iamthesoy/Project-Trousersnake/Images/IMG_2059.jpg

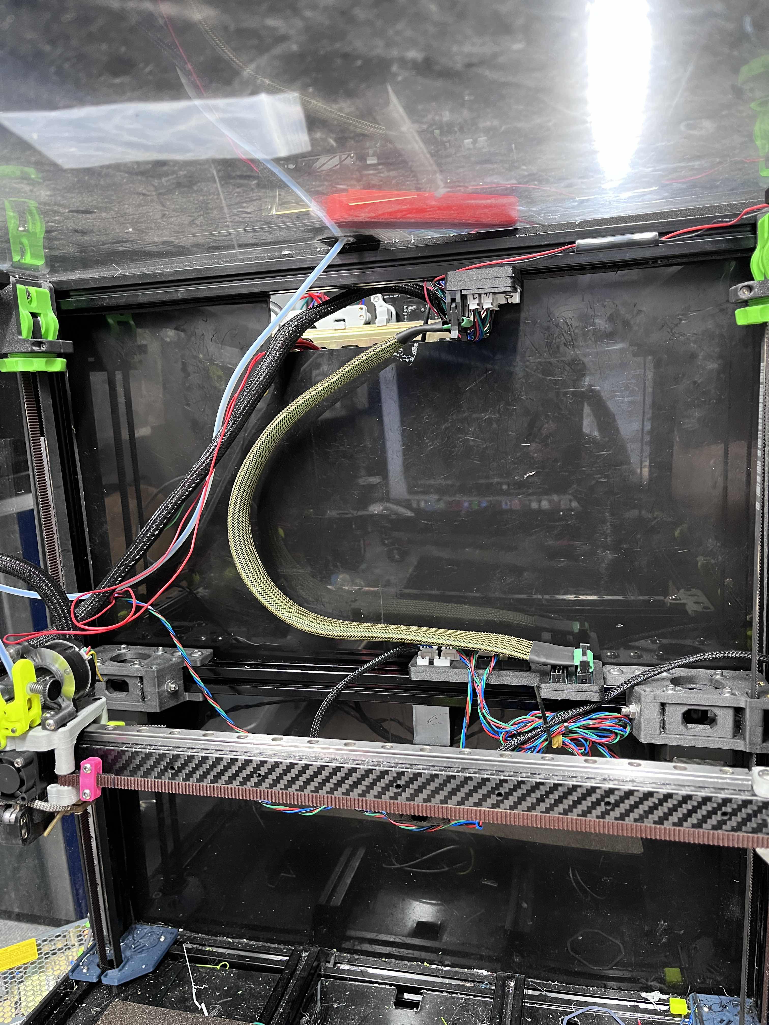
Images/IMG_2059.jpg
